Cristian-O/H2/APP/v2/gateway_real.jpg

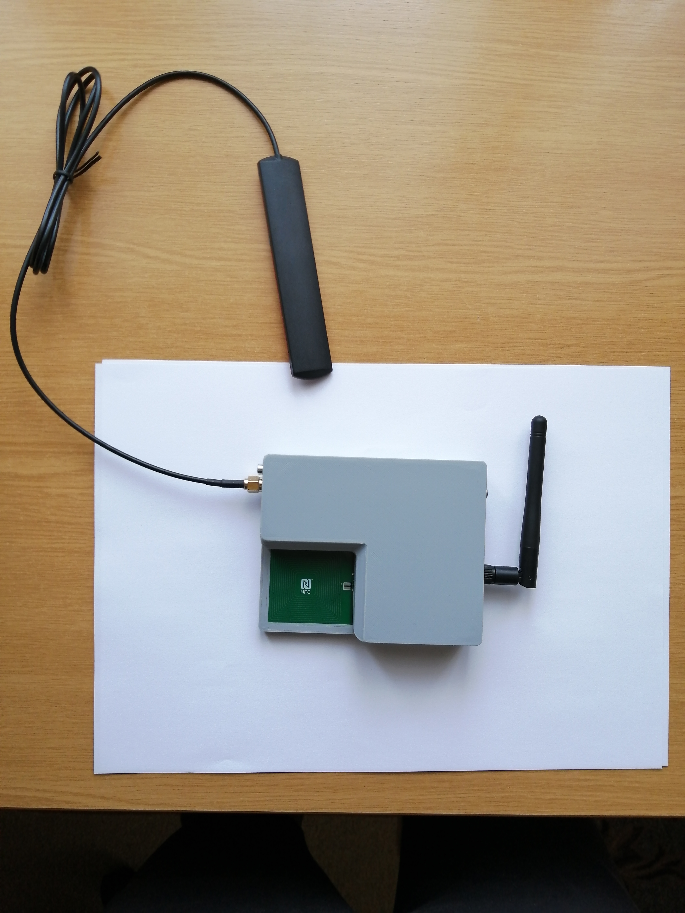
APP/v2/gateway_real.jpg
