Cristian-O/H2/Simulation/NFC_Antenna/antenna_calculation.png

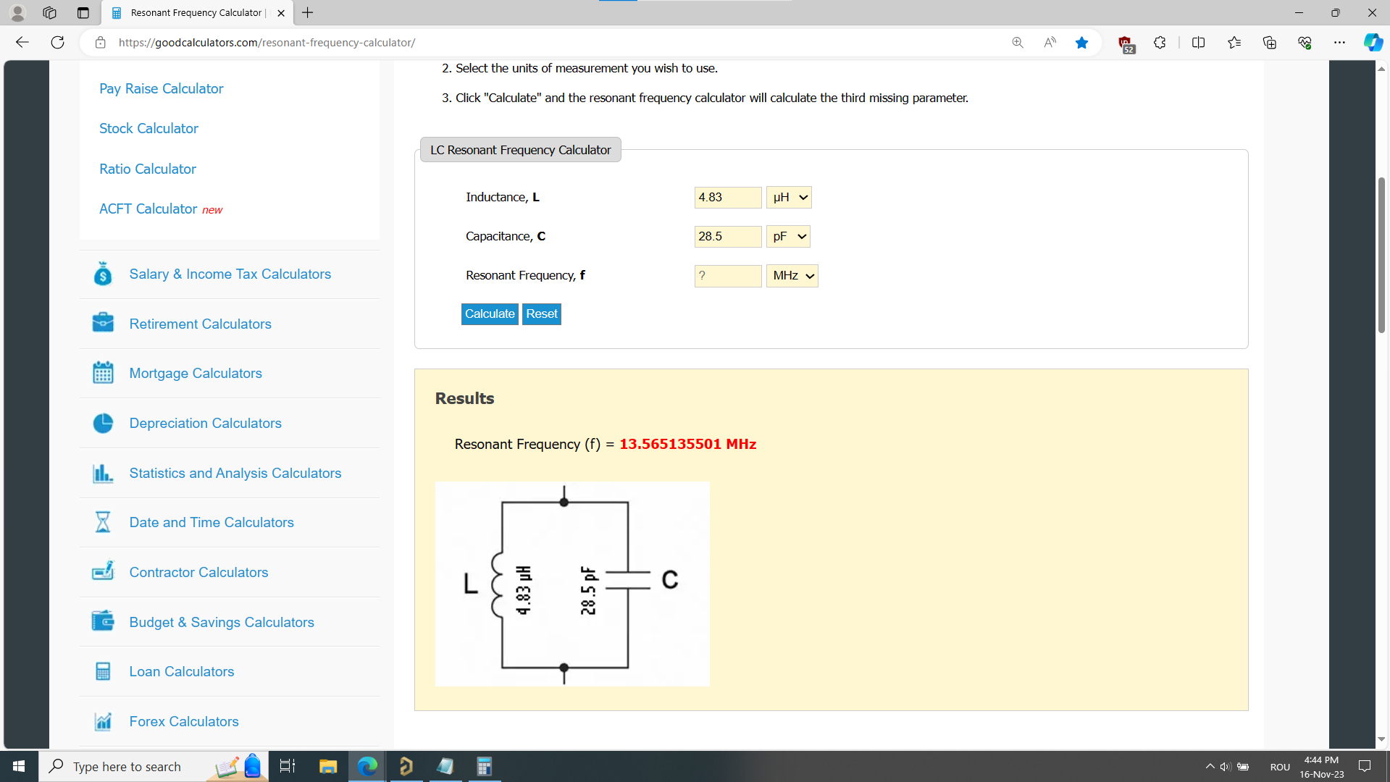
Simulation/NFC_Antenna/antenna_calculation.png
