Cristian-O/H2/CAD/PRODUCTION_FILES/order_PCB_H2.png

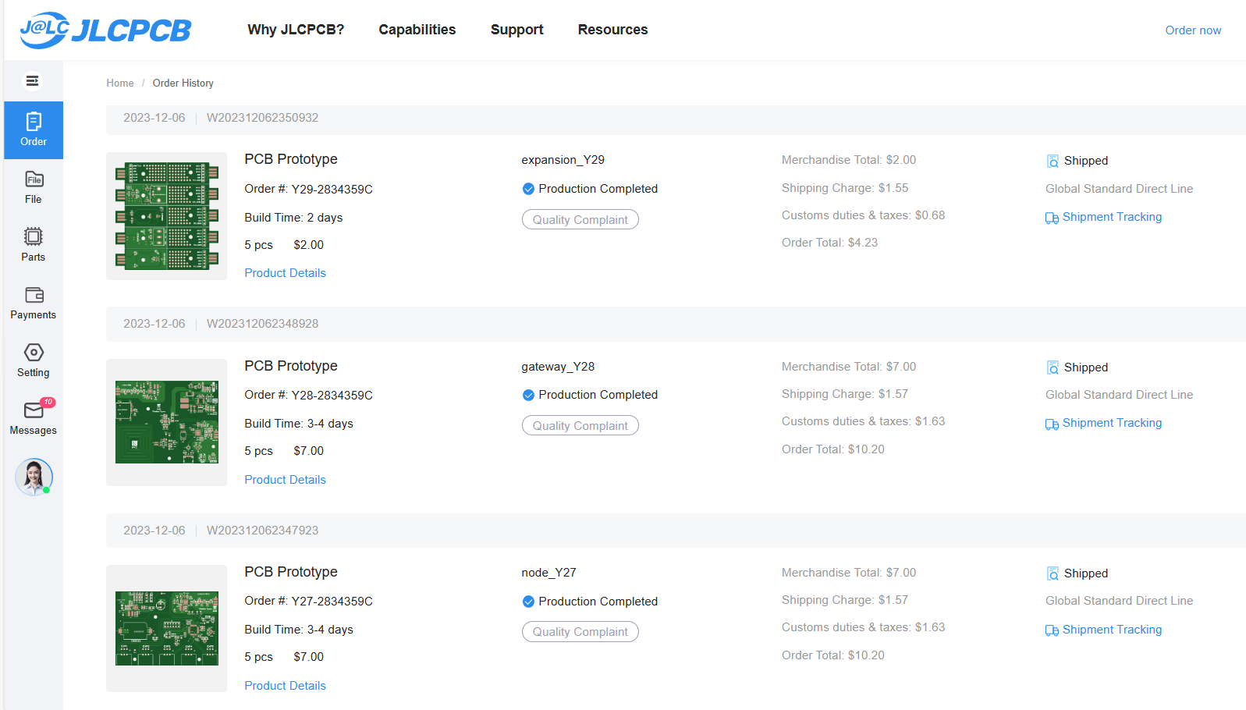
CAD/PRODUCTION_FILES/order_PCB_H2.png
