Cristian-O/H2/Simulation/NFC_Antenna/ant_v16_results.png

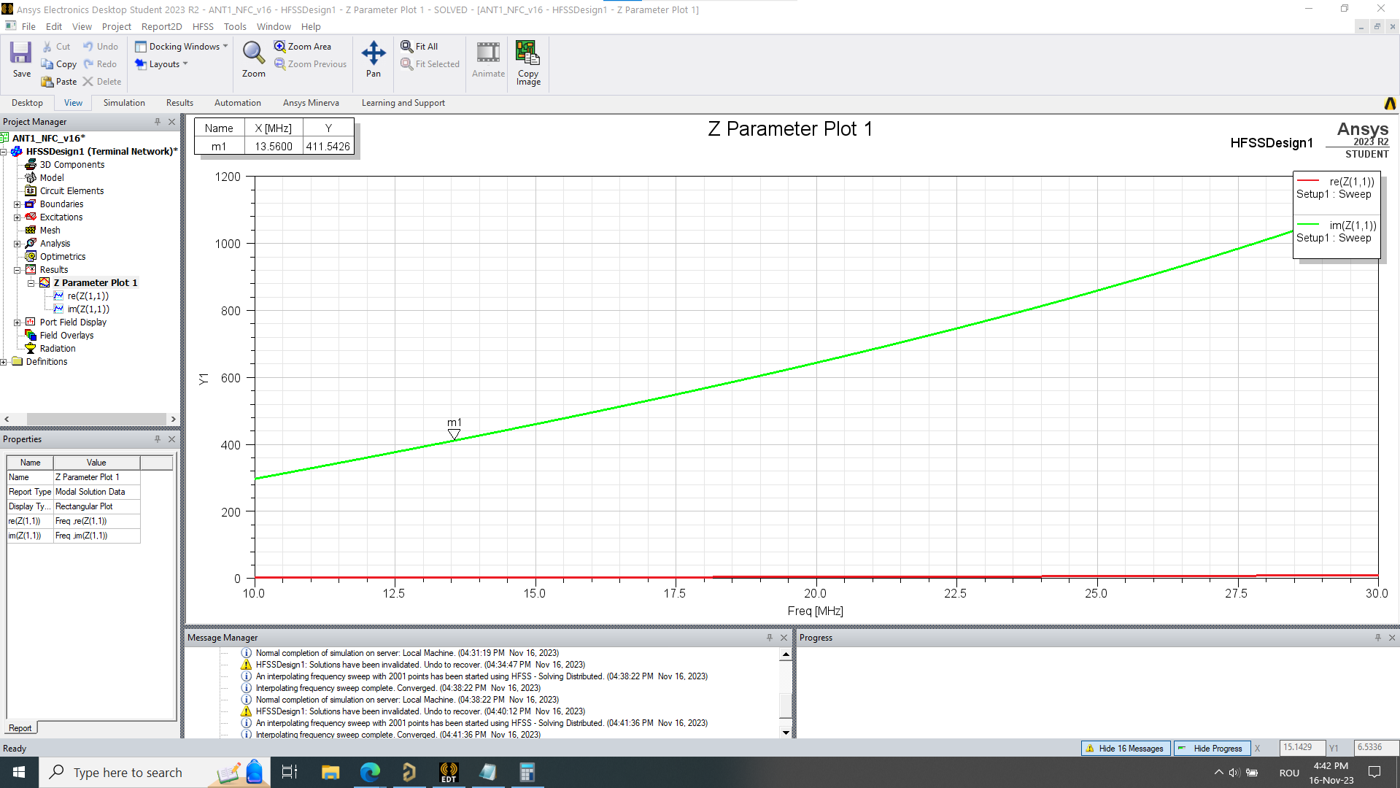
Simulation/NFC_Antenna/ant_v16_results.png
