Cristian-O/H2/Simulation/NFC_Antenna/ant_v16_results_PVC_10mm.png

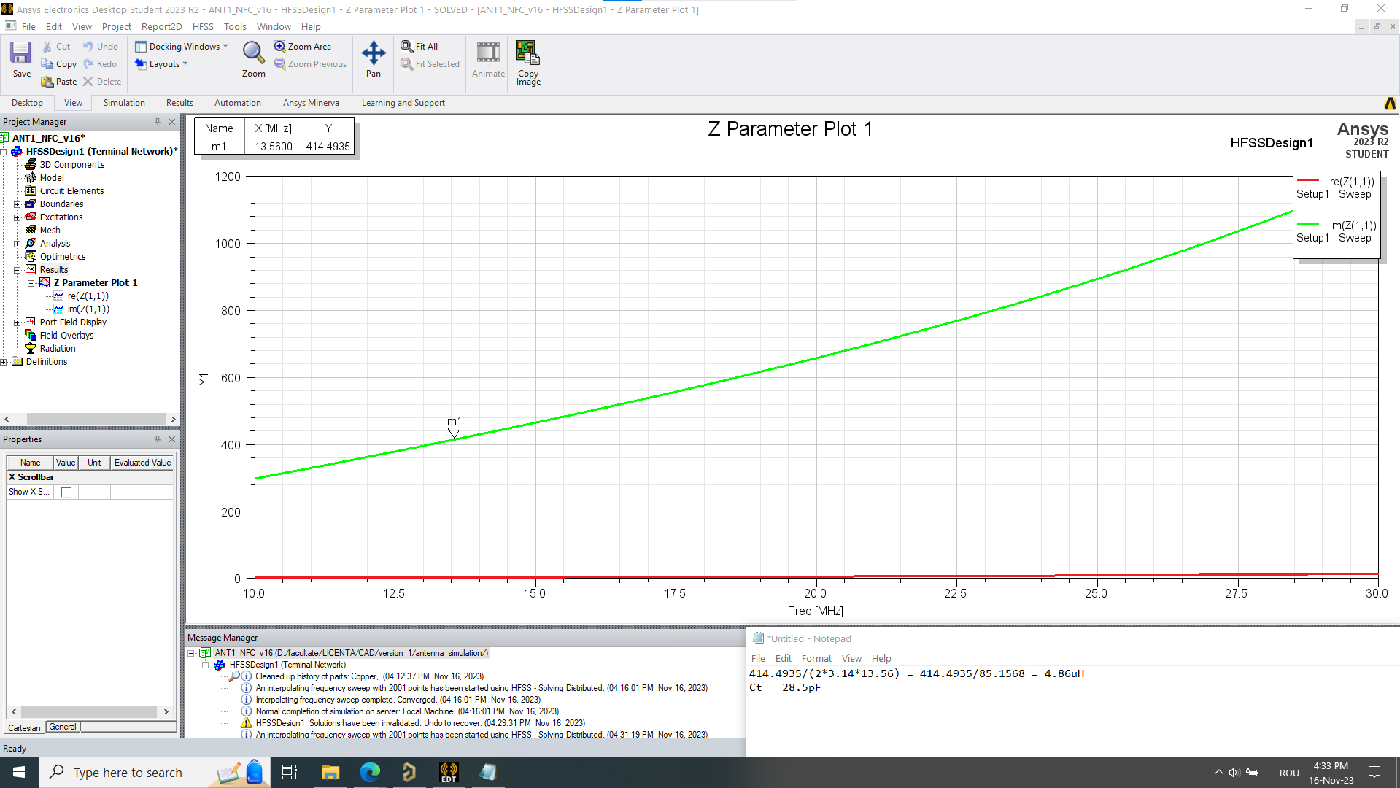
Simulation/NFC_Antenna/ant_v16_results_PVC_10mm.png
